The-hamza-elhakim/RC-Nissan-GTR/Documentation/PCB schematics (KICAD)/AVR.png

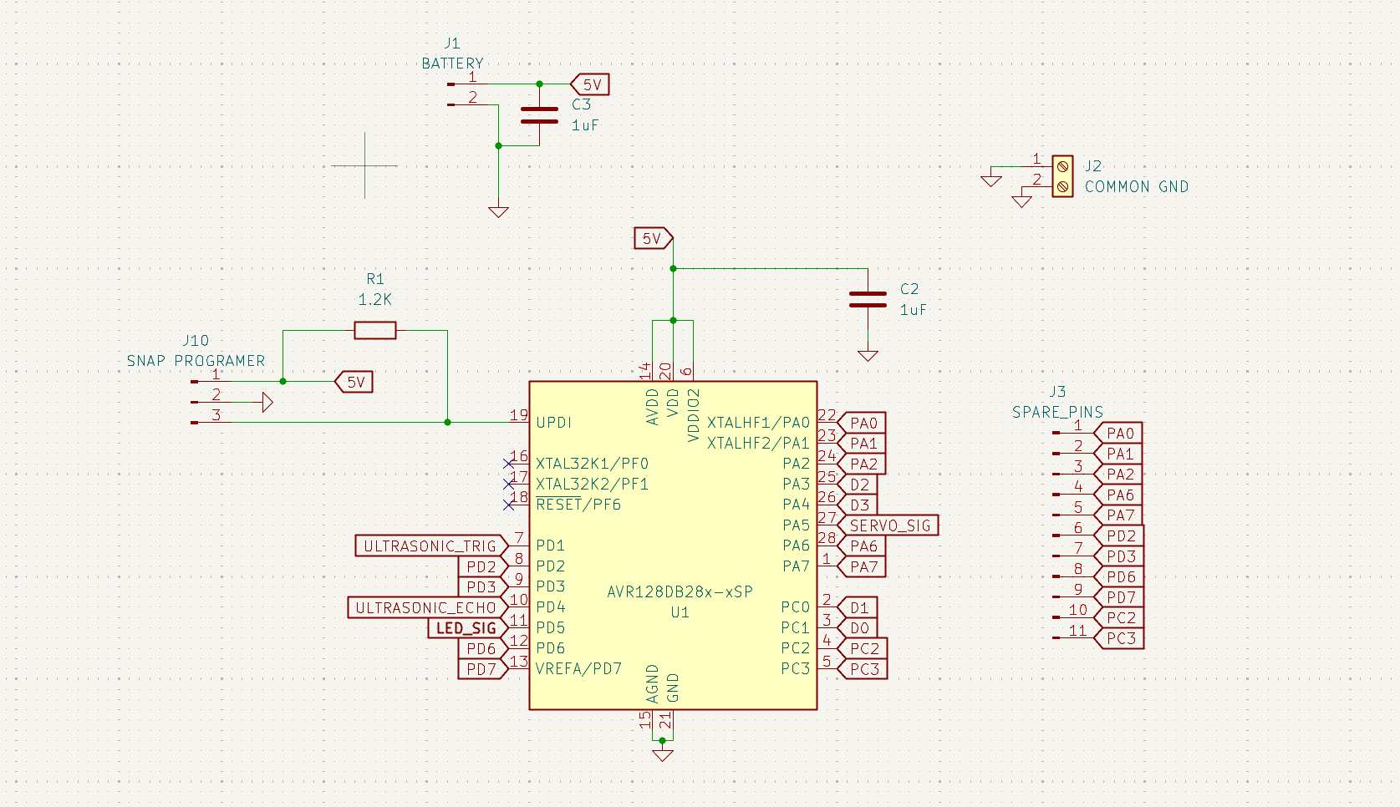
Documentation/PCB schematics (KICAD)/AVR.png
