The-hamza-elhakim/RC-Nissan-GTR/Documentation/PCB schematics (KICAD)/L298N PCB layout.png

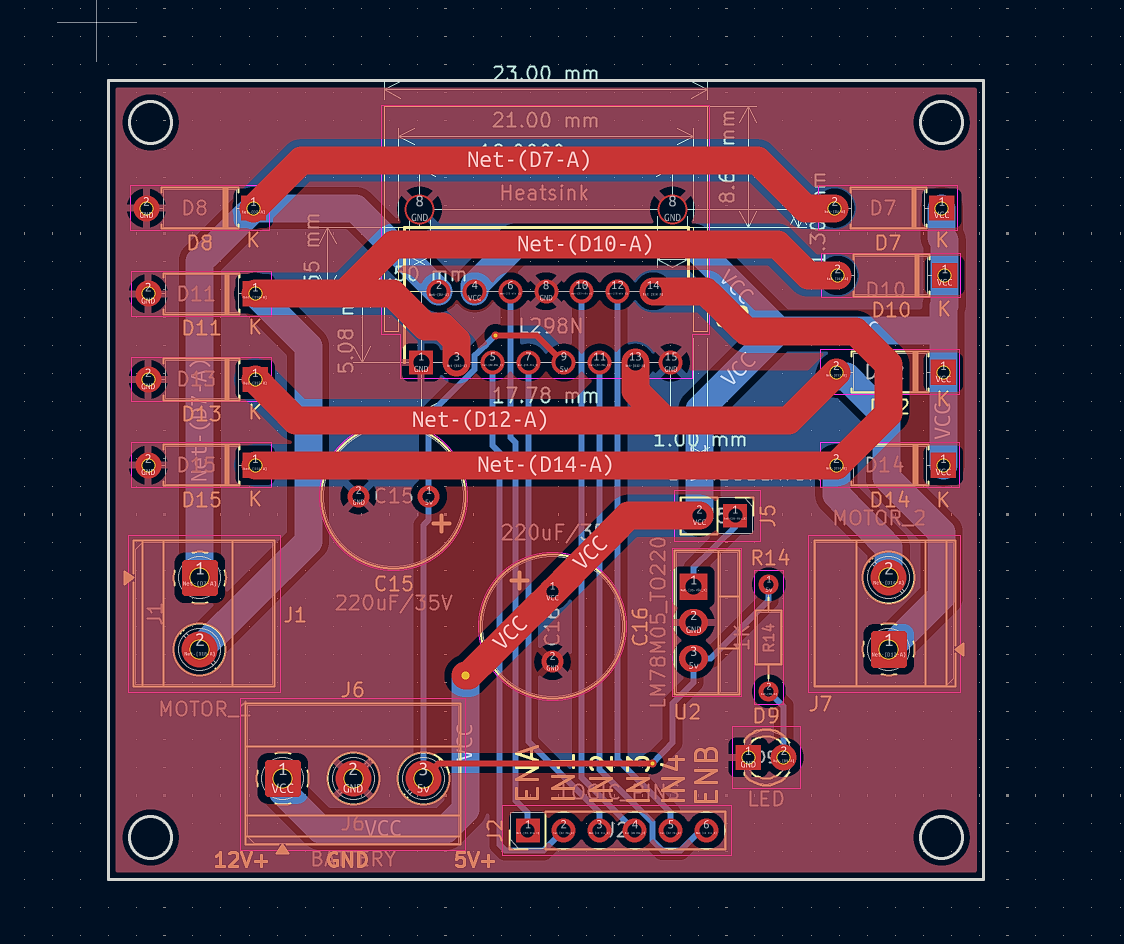
Documentation/PCB schematics (KICAD)/L298N PCB layout.png
