The-hamza-elhakim/RC-Nissan-GTR/Documentation/PCB schematics (KICAD)/L298N.png

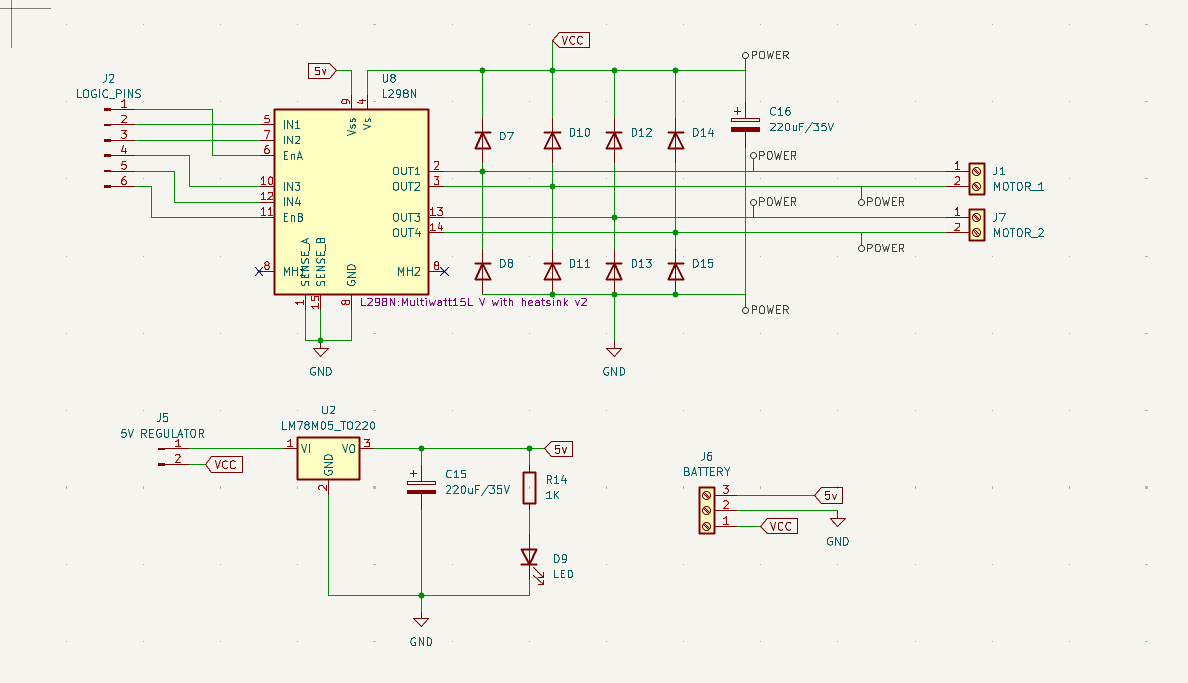
Documentation/PCB schematics (KICAD)/L298N.png
