The-hamza-elhakim/RC-Nissan-GTR/Documentation/PCB schematics (KICAD)/LEDs.png

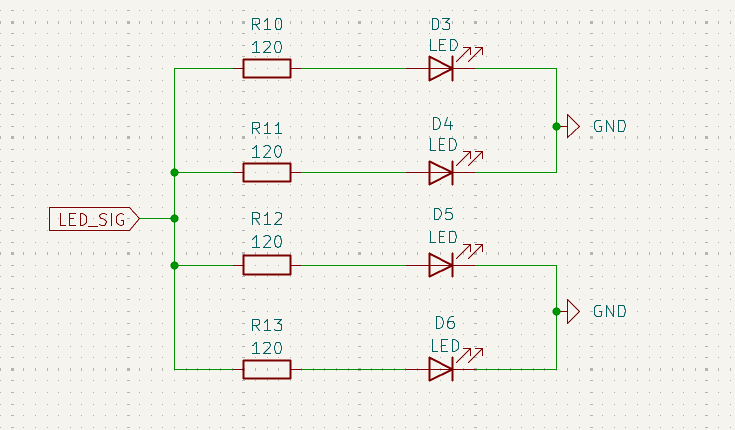
Documentation/PCB schematics (KICAD)/LEDs.png
