The-hamza-elhakim/RC-Nissan-GTR/Documentation/PCB schematics (KICAD)/Main PCB layout.png

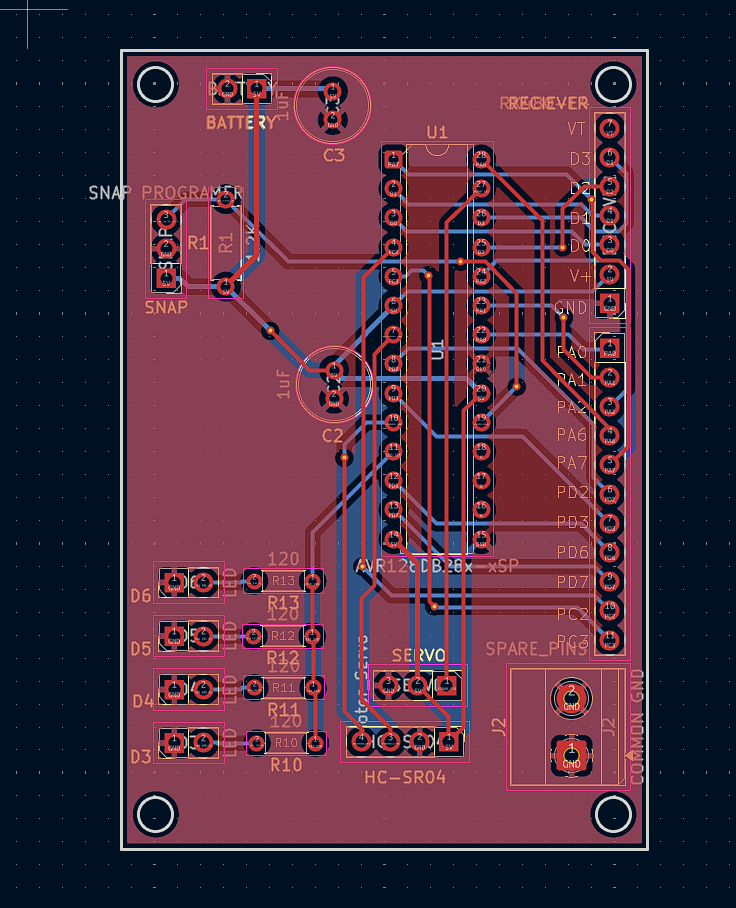
Documentation/PCB schematics (KICAD)/Main PCB layout.png
