The-hamza-elhakim/RC-Nissan-GTR/Documentation/PCB schematics (KICAD)/Screenshot 2025-04-24 224324.png

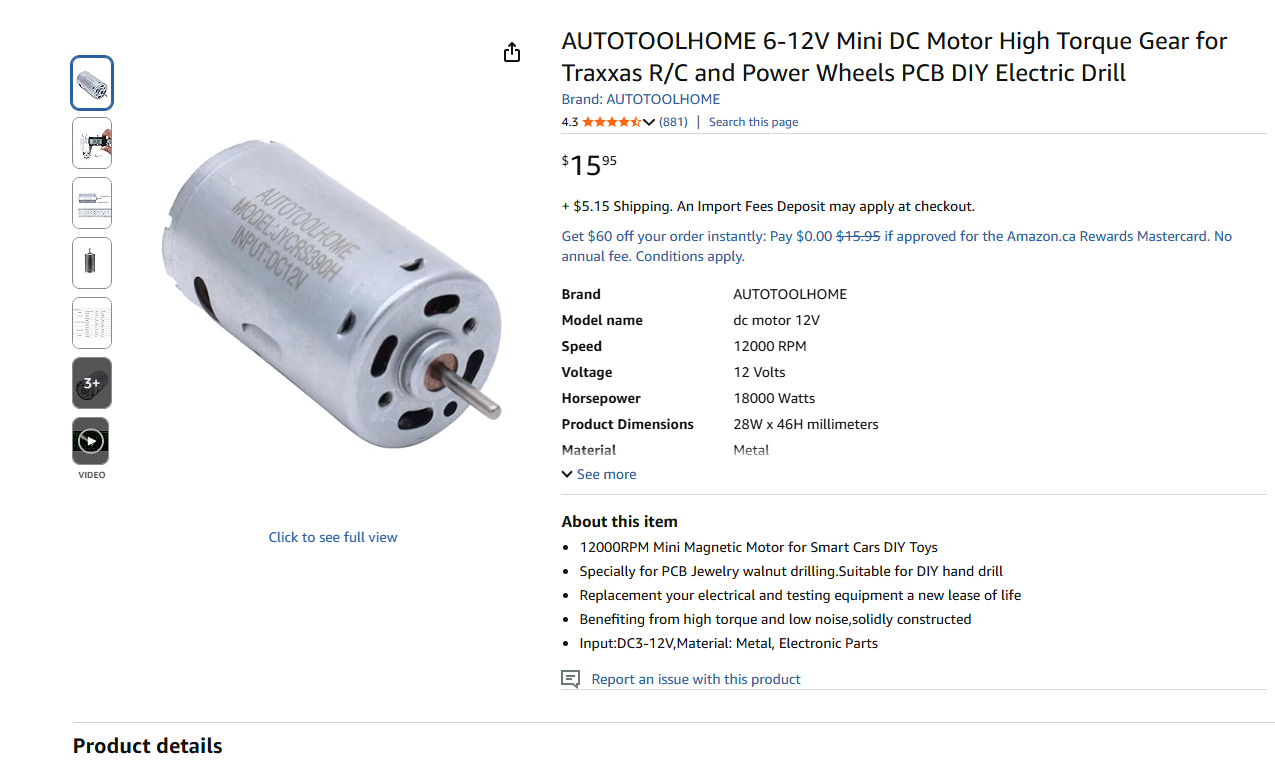
Documentation/PCB schematics (KICAD)/Screenshot 2025-04-24 224324.png
