The-hamza-elhakim/RC-Nissan-GTR/Documentation/PCB schematics (KICAD)/Servo.png

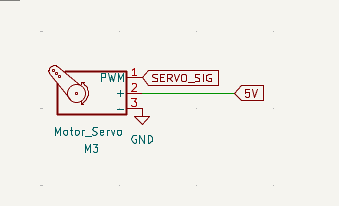
Documentation/PCB schematics (KICAD)/Servo.png
