The-hamza-elhakim/RC-Nissan-GTR/Documentation/PCB schematics (KICAD)/Spare pins.png

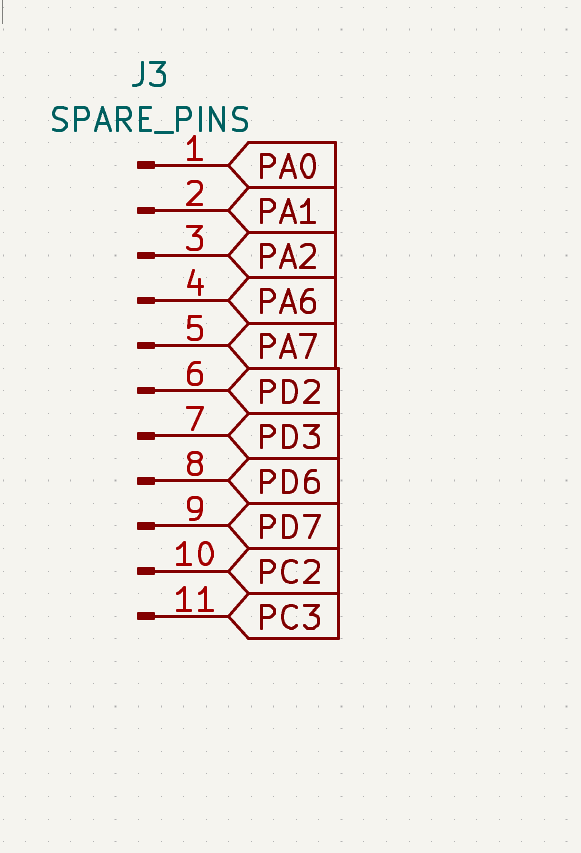
Documentation/PCB schematics (KICAD)/Spare pins.png
