The-hamza-elhakim/RC-Nissan-GTR/Documentation/3D print designs (Fusion 360)/Components.png

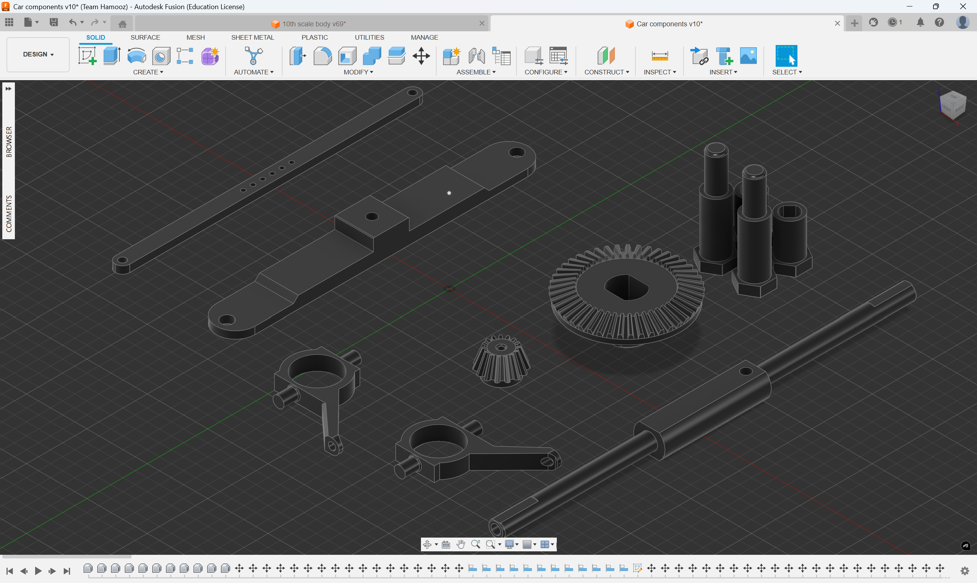
Documentation/3D print designs (Fusion 360)/Components.png
