The-hamza-elhakim/RC-Nissan-GTR/Documentation/3D print designs (Fusion 360)/Top view (components).png

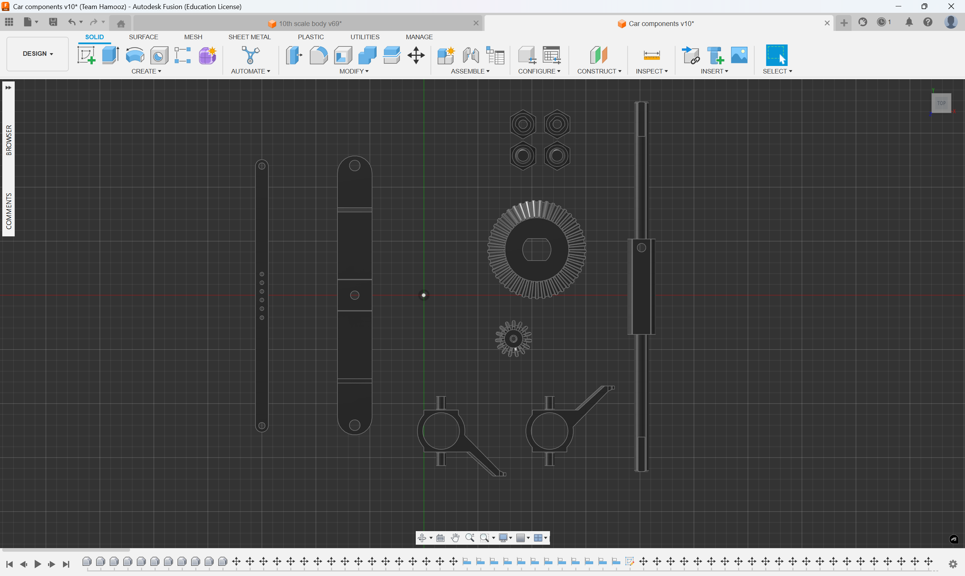
Documentation/3D print designs (Fusion 360)/Top view (components).png
