The-hamza-elhakim/RC-Nissan-GTR/Documentation/3D print designs (Fusion 360)/Front of shell.png

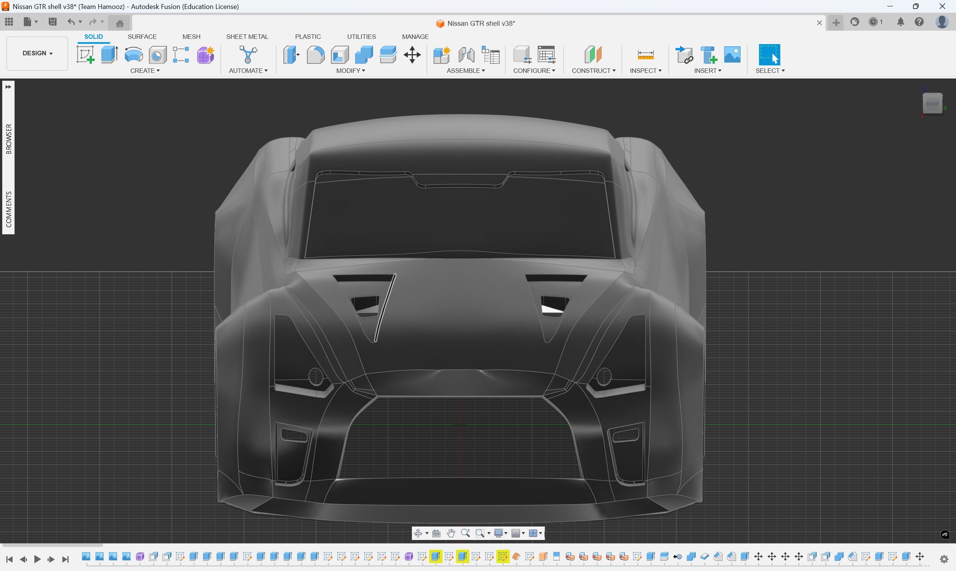
Documentation/3D print designs (Fusion 360)/Front of shell.png
