The-hamza-elhakim/RC-Nissan-GTR/Documentation/3D print designs (Fusion 360)/top of shell.png

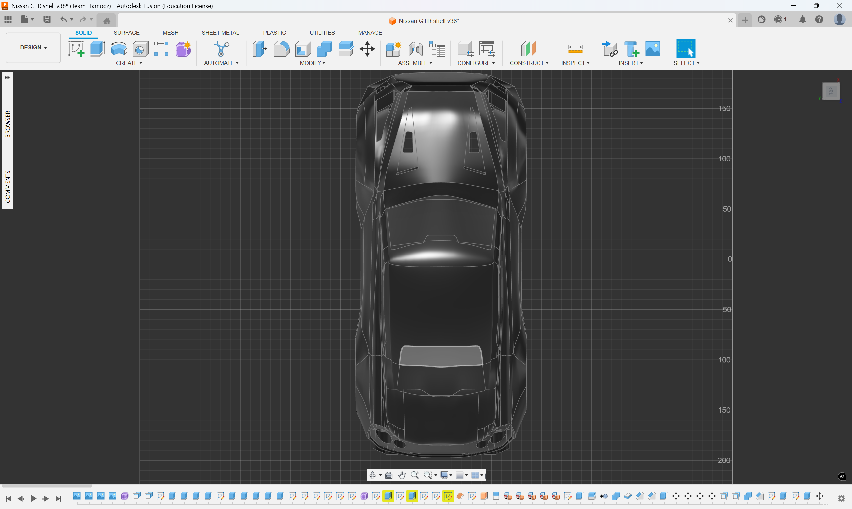
Documentation/3D print designs (Fusion 360)/top of shell.png
