The-hamza-elhakim/RC-Nissan-GTR/Firmware/Car/Car_code.c

#define F_CPU 4000000UL

#include <avr/io.h>
#include <avr/interrupt.h>
#include <util/delay.h>
#include <stdint.h>
#include <stdio.h>


// TM1637 display pins - MODIFIED to use available pins
#define TM1637_CLK_PIN 7  // PD7 (changed from PA2)
#define TM1637_DIO_PIN 6  // PD6 (changed from PA3)
#define TM1637_PORT PORTD // Changed port from PORTA to PORTD

// HC-SR04 sensor pins
#define HC_SR04_TRIG_PIN 1  // PD1
#define HC_SR04_ECHO_PIN 4  // PD4

// Display settings
#define TM1637_BRIGHTNESS 0x0F  // Maximum brightness (0x08 to 0x0F)
#define TM1637_CMD_SET_DATA 0x40
#define TM1637_CMD_SET_ADDR 0xC0
#define TM1637_CMD_DISPLAY_CTRL 0x88  // Display ON with brightness

// 7-segment lookup for digits 0-9
const uint8_t digitToSegment[10] = {
    0x3F, // 0
    0x06, // 1
    0x5B, // 2
    0x4F, // 3
    0x66, // 4
    0x6D, // 5
    0x7D, // 6
    0x07, // 7
    0x7F, // 8
    0x6F  // 9
};

// Timer variables for echo measurement
volatile uint16_t echo_start = 0;
volatile uint16_t echo_end = 0;
volatile uint8_t echo_done = 0;

// Moving average filter variables
#define FILTER_SIZE 5
uint16_t distance_buffer[FILTER_SIZE] = {0};
uint8_t buffer_index = 0;
uint8_t buffer_filled = 0;

// Function prototypes
void tm1637_start(void);
void tm1637_stop(void);
void tm1637_write_byte(uint8_t b);
void tm1637_init(void);
void tm1637_display(uint8_t segments[]);

void timer_init(void);
void trigger_measurement(void);
uint16_t calculate_distance(void);
uint16_t apply_moving_average(uint16_t new_distance);
void display_distance(uint16_t distance);

// Timer overflow interrupt
ISR(TCB0_INT_vect) {   
    // This interrupt will trigger if the echo is too long
    // Reset everything for the next measurement
    TCB0.INTFLAGS = TCB_OVF_bm; // Clear the interrupt flag
    echo_done = 1;
}

// Pin change interrupt for echo pin
ISR(PORTD_PORT_vect) {
    // Check if it's the echo pin
    if (PORTD.INTFLAGS & (1 << HC_SR04_ECHO_PIN)) {
        // If echo pin is high, start the timer
        if (PORTD.IN & (1 << HC_SR04_ECHO_PIN)) {
            TCB0.CNT = 0; // Reset counter
            echo_start = 0;
            TCB0.CTRLA |= TCB_ENABLE_bm; // Start timer
        } 
        // If echo pin is low, stop the timer and calculate the pulse duration
        else {
            echo_end = TCB0.CNT;
            TCB0.CTRLA &= ~TCB_ENABLE_bm; // Stop timer
            echo_done = 1;
        }
        PORTD.INTFLAGS = (1 << HC_SR04_ECHO_PIN); // Clear the interrupt flag
    }
}

void timer_init(void) {
    // Configure TCB0 for microsecond timing
    // At 4MHz, with prescaler 2, each tick is 0.5us
    TCB0.CTRLA = TCB_CLKSEL_DIV2_gc;// Select DIV2 prescaler
    TCB0.CTRLB = TCB_CNTMODE_INT_gc;    // Select periodic interrupt mode
    TCB0.CCMP = 60000;                  // Set overflow value (30ms timeout)
    TCB0.INTCTRL = TCB_OVF_bm;          // Enable overflow interrupt
    // Timer is enabled in the ISR when echo pin goes high
}

void trigger_measurement(void) {
    // Make sure timer is stopped and interrupts are cleared
    TCB0.CTRLA &= ~TCB_ENABLE_bm;
    TCB0.INTFLAGS = TCB_OVF_bm;
    
    // Clear interrupt flag for ECHO pin
    PORTD.INTFLAGS = (1 << HC_SR04_ECHO_PIN);
    
    // Send a 10us pulse to TRIG pin
    PORTD.OUTSET = (1 << HC_SR04_TRIG_PIN);
    _delay_us(10);
    PORTD.OUTCLR = (1 << HC_SR04_TRIG_PIN);
}

uint16_t calculate_distance(void) {
    // If no echo was received or timer overflowed
    if (echo_end == 0) {
        return 0;
    }
    
    uint16_t pulse_duration = echo_end;
    
    // Convert pulse duration to distance in cm
    // Sound travels at ~343m/s = 34300cm/s = 0.0343cm/us
    // Distance = (Time × Speed of Sound) ÷ 2
    // With 0.5us per timer tick: Distance = pulse_duration × 0.5 × 0.0343 ÷ 2
    // Simplified: Distance = pulse_duration × 0.008575 (approx)
    // To avoid floating point: Distance = pulse_duration ÷ 116.6 (approx)
    
    uint16_t distance = pulse_duration / 117;
    
    // Limit max distance to 400cm (HC-SR04 max range)
    if (distance > 400) {
        distance = 0; // Out of range
    }
    
    return distance;
}

uint16_t apply_moving_average(uint16_t new_distance) {
    // Add new distance to buffer
    distance_buffer[buffer_index] = new_distance;
    
    // Update buffer index
    buffer_index = (buffer_index + 1) % FILTER_SIZE;
    
    // Update buffer filled status
    if (buffer_index == 0) {
        buffer_filled = 1;
    }
    
    // Calculate average
    uint32_t sum = 0;
    uint8_t count = buffer_filled ? FILTER_SIZE : buffer_index;
    
    for (uint8_t i = 0; i < count; i++) {
        sum += distance_buffer[i];
    }
    
    // Return average (prevent division by zero)
    return (count > 0) ? (uint16_t)(sum / count) : 0;
}

void tm1637_init(void) {
    _delay_ms(50);  // Let display stabilize
    
    // Set data command (automatic address increment + normal mode)
    tm1637_start();
    tm1637_write_byte(TM1637_CMD_SET_DATA);
    tm1637_stop();
    
    // Set display ON with brightness
    tm1637_start();
    tm1637_write_byte(TM1637_CMD_DISPLAY_CTRL | (TM1637_BRIGHTNESS & 0x07));
    tm1637_stop();
    
    // Clear display initially
    uint8_t clear_segments[4] = {0, 0, 0, 0};
    tm1637_display(clear_segments);
}

void tm1637_display(uint8_t segments[]) {
    tm1637_start();
    tm1637_write_byte(TM1637_CMD_SET_ADDR);  // Set starting address to 0
    
    for(uint8_t i = 0; i < 4; i++) {
        tm1637_write_byte(segments[i]);
    }
    
    tm1637_stop();
}

void tm1637_start(void) {
    // MODIFIED: Changed PORTA to TM1637_PORT (PORTD)
    TM1637_PORT.OUTSET = (1 << TM1637_DIO_PIN);
    TM1637_PORT.OUTSET = (1 << TM1637_CLK_PIN);
    _delay_us(2);
    TM1637_PORT.OUTCLR = (1 << TM1637_DIO_PIN);
    _delay_us(2);
    TM1637_PORT.OUTCLR = (1 << TM1637_CLK_PIN);
    _delay_us(2);
}

void tm1637_stop(void) {
    // MODIFIED: Changed PORTA to TM1637_PORT (PORTD)
    TM1637_PORT.OUTCLR = (1 << TM1637_CLK_PIN);
    _delay_us(2);
    TM1637_PORT.OUTCLR = (1 << TM1637_DIO_PIN);
    _delay_us(2);
    TM1637_PORT.OUTSET = (1 << TM1637_CLK_PIN);
    _delay_us(2);
    TM1637_PORT.OUTSET = (1 << TM1637_DIO_PIN);
    _delay_us(2);
}

void tm1637_write_byte(uint8_t b) {
    // MODIFIED: Changed PORTA to TM1637_PORT (PORTD)
    for(uint8_t i = 0; i < 8; i++) {
        TM1637_PORT.OUTCLR = (1 << TM1637_CLK_PIN);
        _delay_us(2);
        
        if(b & 0x01)
            TM1637_PORT.OUTSET = (1 << TM1637_DIO_PIN);
        else
            TM1637_PORT.OUTCLR = (1 << TM1637_DIO_PIN);
        
        _delay_us(2);
        TM1637_PORT.OUTSET = (1 << TM1637_CLK_PIN);
        _delay_us(2);
        b >>= 1;
    }
    
    // Wait for ACK
    TM1637_PORT.OUTCLR = (1 << TM1637_CLK_PIN);
    TM1637_PORT.DIRCLR = (1 << TM1637_DIO_PIN);  // Set DIO as input for ACK
    _delay_us(5);
    
    // Read ACK (not used but proper protocol)
    // uint8_t ack = !(TM1637_PORT.IN & (1 << TM1637_DIO_PIN));
    
    TM1637_PORT.OUTSET = (1 << TM1637_CLK_PIN);
    _delay_us(2);
    TM1637_PORT.OUTCLR = (1 << TM1637_CLK_PIN);
    
    TM1637_PORT.DIRSET = (1 << TM1637_DIO_PIN);  // Set DIO back to output
    _delay_us(2);
}

void display_distance(uint16_t distance) {
    // Break the distance into 4 digits
    uint8_t digits[4];
    digits[0] = (distance / 1000) % 10;
    digits[1] = (distance / 100) % 10;
    digits[2] = (distance / 10) % 10;
    digits[3] = distance % 10;
    
    // Convert to segments
    uint8_t segments[4];
    for(uint8_t i = 0; i < 4; i++) {
        segments[i] = digitToSegment[digits[i]];
    }
    
    // Don't show leading zeros
    if(distance < 1000) segments[0] = 0;
    if(distance < 100) segments[1] = 0;
    if(distance < 10) segments[2] = 0;
    
    // Always show at least one digit
    if(distance == 0) segments[3] = digitToSegment[0];
    
    // Display the segments
    tm1637_display(segments);
}

int main(void) {
    // Set clock to 4MHz using internal high-frequency oscillator with prescaler
    CLKCTRL.MCLKCTRLA = CLKCTRL_CLKSEL_OSCHF_gc;
    CLKCTRL.MCLKCTRLB = CLKCTRL_PDIV_4X_gc | CLKCTRL_PEN_bm;
    
    // Setup TM1637 pins (PD7, PD6) as outputs and set high - MODIFIED
    PORTD.DIRSET = (1 << TM1637_CLK_PIN) | (1 << TM1637_DIO_PIN);
    PORTD.OUTSET = (1 << TM1637_CLK_PIN) | (1 << TM1637_DIO_PIN);
    
    // Setup HC-SR04 sensor pins: TRIG (PD1) as output, ECHO (PD4) as input
    PORTD.DIRSET = (1 << HC_SR04_TRIG_PIN);
    PORTD.DIRCLR = (1 << HC_SR04_ECHO_PIN);
    PORTD.OUTCLR = (1 << HC_SR04_TRIG_PIN); // Ensure TRIG is initially low
    
    // Configure pin interrupt for ECHO pin
    PORTD.PIN4CTRL = PORT_PULLUPEN_bm | PORT_ISC_BOTHEDGES_gc; // Pull-up enabled, interrupt on both edges
    
    // Initialize timer for echo measurement
    timer_init();
    
    // Initialize display
    tm1637_init();
    
    // Allow sensor to settle on startup
    _delay_ms(500);
    
    // Enable global interrupts
    sei();
    
    uint16_t distance_cm;
    
    // Display zero initially
    display_distance(0);
    
    while(1) {
        // === HC-SR04 Distance Measurement ===
        
        // Trigger a new measurement
        trigger_measurement();
        while(!echo_done);
        distance_cm = calculate_distance();
        distance_cm = apply_moving_average(distance_cm);
        display_distance(distance_cm);
        echo_done = 0;
  
        _delay_ms(100);
    }
    
    return 0;
}
