The-hamza-elhakim/RC-Nissan-GTR/Documentation/Back.JPG

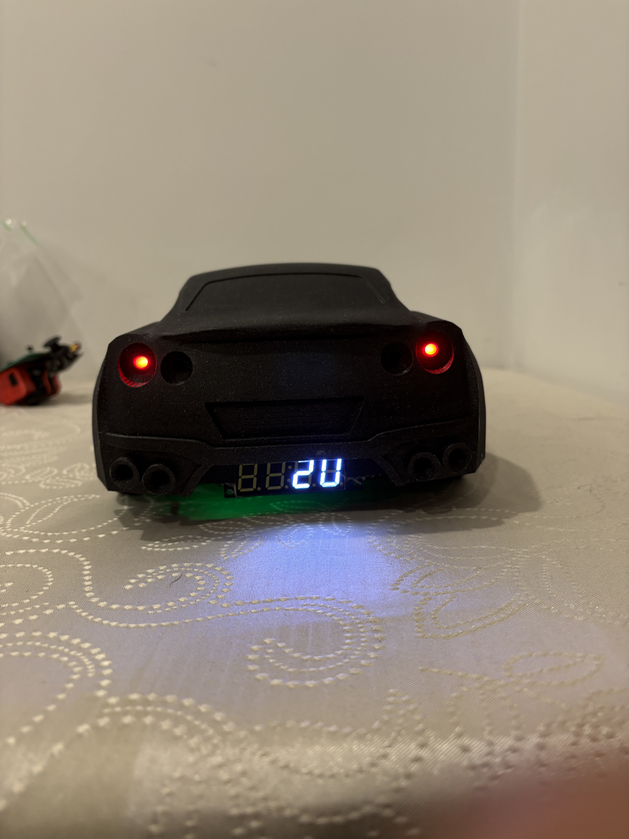
Documentation/Back.JPG
