The-hamza-elhakim/RC-Nissan-GTR/Documentation/IFX007t .JPG

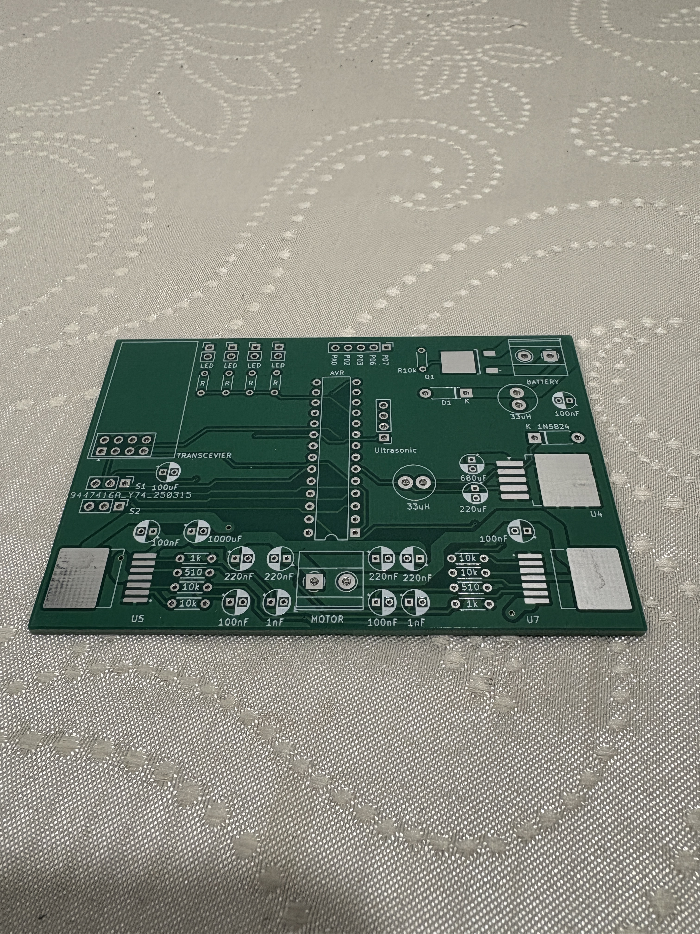
Documentation/IFX007t .JPG
