The-hamza-elhakim/RC-Nissan-GTR/Documentation/IFX007t concept PCB.JPG

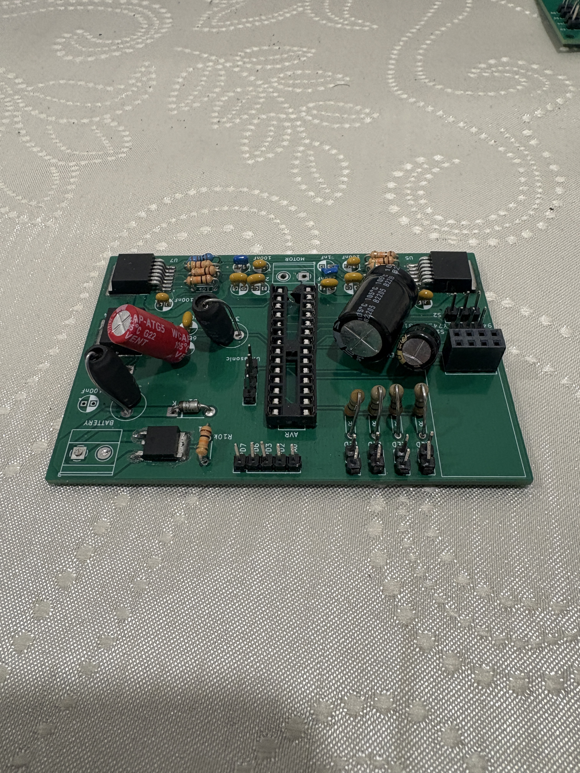
Documentation/IFX007t concept PCB.JPG
