The-hamza-elhakim/RC-Nissan-GTR/Documentation/Main PCB with AVR.JPG

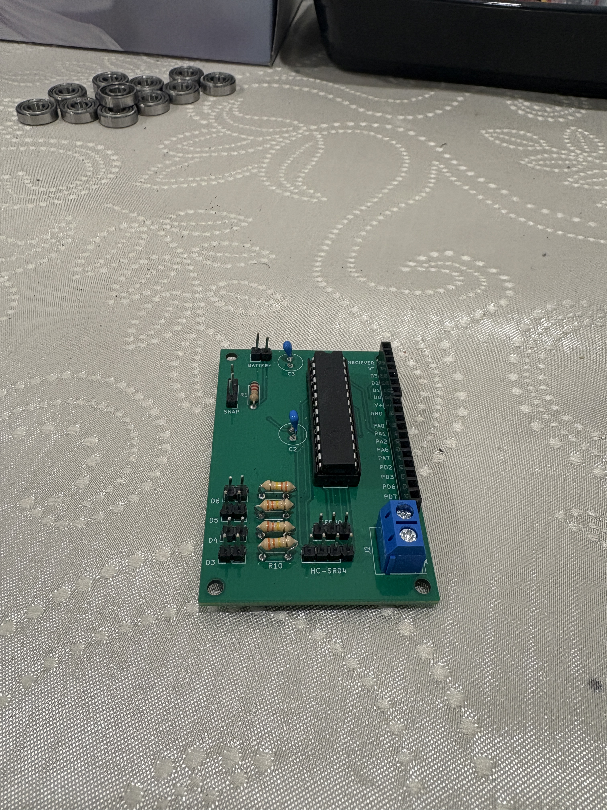
Documentation/Main PCB with AVR.JPG
