The-hamza-elhakim/RC-Nissan-GTR/Documentation/Nissan GTR.JPG

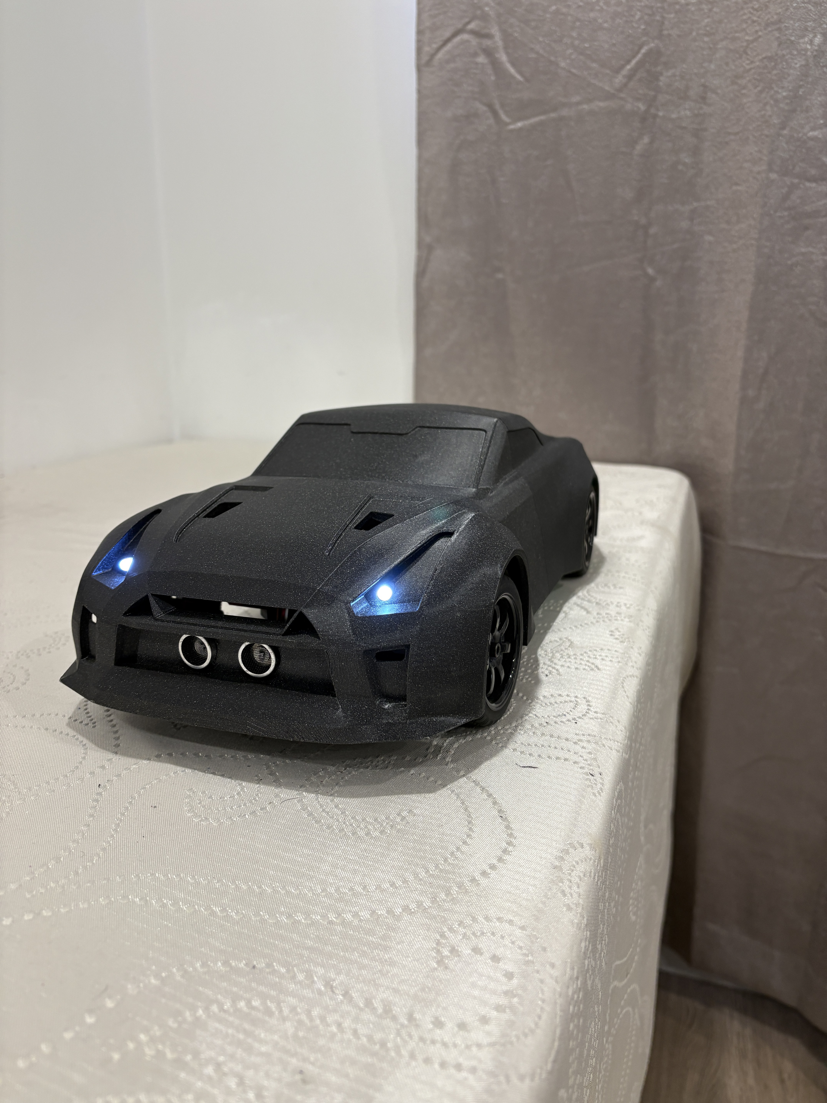
Documentation/Nissan GTR.JPG
